ye-zhang0720/MagicBox/Software/Magic_Box/src/app/weather/weather_image.h

#ifndef __WEATHER_IMAGE_H
#define __WEATHER_IMAGE_H

#if __has_include("lvgl.h")
#include "lvgl.h"
#else
#include "lvgl/lvgl.h"
#endif

#ifndef LV_ATTRIBUTE_MEM_ALIGN
#define LV_ATTRIBUTE_MEM_ALIGN
#endif
#ifndef LV_ATTRIBUTE_IMG_WEATHER
#define LV_ATTRIBUTE_IMG_WEATHER
#endif
#ifndef LV_ATTRIBUTE_IMG_MAN
#define LV_ATTRIBUTE_IMG_MAN
#endif

const LV_ATTRIBUTE_MEM_ALIGN LV_ATTRIBUTE_IMG_WEATHER uint8_t tempImg_map[] = {
#if LV_COLOR_DEPTH == 1 || LV_COLOR_DEPTH == 8
	/*Pixel format: Red: 3 bit, Green: 3 bit, Blue: 2 bit*/
	0x00, 0x00, 0x00, 0x00, 0x00, 0x00, 0x00, 0x00, 0x00, 0x00, 0x00, 0x00, 0x00, 0x00, 0x00, 0x00, 0x00, 0x00,
	0x00, 0x00, 0x00, 0x00, 0x00, 0x00, 0x00, 0x00, 0xf6, 0xf6, 0x00, 0x00, 0x00, 0x00, 0x00, 0x00, 0x00, 0x00,
	0x00, 0x00, 0x00, 0x00, 0xf6, 0x00, 0x00, 0x00, 0xf6, 0xf6, 0x00, 0x00, 0x00, 0xf6, 0x00, 0x00, 0x00, 0x00,
	0x00, 0x00, 0x00, 0x00, 0xf6, 0xf6, 0x00, 0x00, 0xf6, 0xf6, 0x00, 0x00, 0xf6, 0xf6, 0x00, 0x00, 0x00, 0x00,
	0x00, 0x00, 0x00, 0x00, 0xf6, 0xf6, 0x00, 0x00, 0xfe, 0xfe, 0x00, 0x00, 0xf6, 0xf6, 0x00, 0x00, 0x00, 0x00,
	0xfa, 0xf6, 0x00, 0x00, 0x00, 0x00, 0xff, 0xff, 0xff, 0xff, 0xff, 0xff, 0x00, 0x00, 0x00, 0x00, 0xf6, 0xfa,
	0xff, 0xf6, 0xf6, 0x00, 0x00, 0xff, 0xff, 0xff, 0xff, 0xff, 0xff, 0xff, 0xff, 0x00, 0x00, 0xf6, 0xf6, 0xfc,
	0x00, 0x00, 0xf6, 0x00, 0x00, 0xff, 0xff, 0xff, 0xff, 0xff, 0xff, 0xff, 0xff, 0x00, 0x00, 0xf6, 0x00, 0x00,
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
};

const lv_img_dsc_t man_3 = {
  .header.always_zero = 0,
  .header.w = 80,
  .header.h = 80,
  .data_size = 1617,
  .header.cf = LV_IMG_CF_INDEXED_2BIT,
  .data = man_3_map,
};
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
