ye-zhang0720/MagicBox/Software/Magic_Box/src/common.cpp

#include "common.h"
#include "network.h"

IMU mpu;
SdCard tf;
Pixel rgb;
// Config g_cfg;       // 全局配置文件
Network g_network;  // 网络连接
FlashFS g_flashCfg; // flash中的文件系统（替代原先的Preferences）
Display screen;     // 屏幕对象
/*
  BH1750 can be physically configured to use two I2C addresses:
    - 0x23 (most common) (if ADD pin had < 0.7VCC voltage)
    - 0x5C (if ADD pin had > 0.7VCC voltage)

  Library uses 0x23 address as default, but you can define any other address.
  If you had troubles with default value - try to change it to 0x5C.

*/
BH1750 lightMeter(0x23);   // 光线传感器对象
float lux = 0;
System_information *systemInfo;



// lvgl handle的锁
SemaphoreHandle_t lvgl_mutex = xSemaphoreCreateMutex();

boolean doDelayMillisTime(unsigned long interval, unsigned long *previousMillis, boolean state)
{
    unsigned long currentMillis = GET_SYS_MILLIS();
    if (currentMillis - *previousMillis >= interval)
    {
        *previousMillis = currentMillis;
        state = !state;
    }
    return state;
}

#if GFX

#include <Arduino_GFX_Library.h>

Arduino_HWSPI *bus = new Arduino_HWSPI(TFT_DC /* DC */, TFT_CS /* CS */, TFT_SCLK, TFT_MOSI, TFT_MISO);
Arduino_ST7789 *tft = new Arduino_ST7789(bus, TFT_RST /* RST */, 3 /* rotation */, true /* IPS */,
                                         240 /* width */, 240 /* height */,
                                         0 /* col offset 1 */, 80 /* row offset 1 */);

#else
#include <TFT_eSPI.h>
/*
TFT pins should be set in path/to/Arduino/libraries/TFT_eSPI/User_Setups/Setup24_ST7789.h
*/
TFT_eSPI scre = TFT_eSPI(SCREEN_HOR_RES, SCREEN_VER_RES);
TFT_eSPI *tft;


#endif
