ye-zhang0720/MagicBox/Software/Magic_Box/src/app/game_2048/game_2048_gui.h

#ifndef APP_GAME_2048_GUI_H
#define APP_GAME_2048_GUI_H

#ifdef __cplusplus
extern "C"
{
#endif

#include "lvgl.h"

#define ANIEND_WAIT                 \
    while (lv_anim_count_running()) \
        lv_task_handler(); // 等待动画完成

    void game_2048_gui_init(void);
    void display_game_2048(const char *file_name, lv_scr_load_anim_t anim_type);
    void game_2048_gui_del(void);

	const lv_img_dsc_t* getN(int i);
	void showBoard(int* map);
	void showAnim(int* animMap, int direction);
    void showNewBorn(int newborn, int *map);
	void born(int i);
    void show_result_messageBox(char *result);
    void close_result_messageBox();

#ifdef __cplusplus
} /* extern "C" */
#endif


#ifdef __cplusplus
extern "C"
{
#endif

#include "lvgl.h"
    extern const lv_img_dsc_t app_game_2048;

#ifdef __cplusplus
} /* extern "C" */
#endif

#endif
